Charles-pyt/My-Home-Assisant-Box/Checkout/Raspberry.png

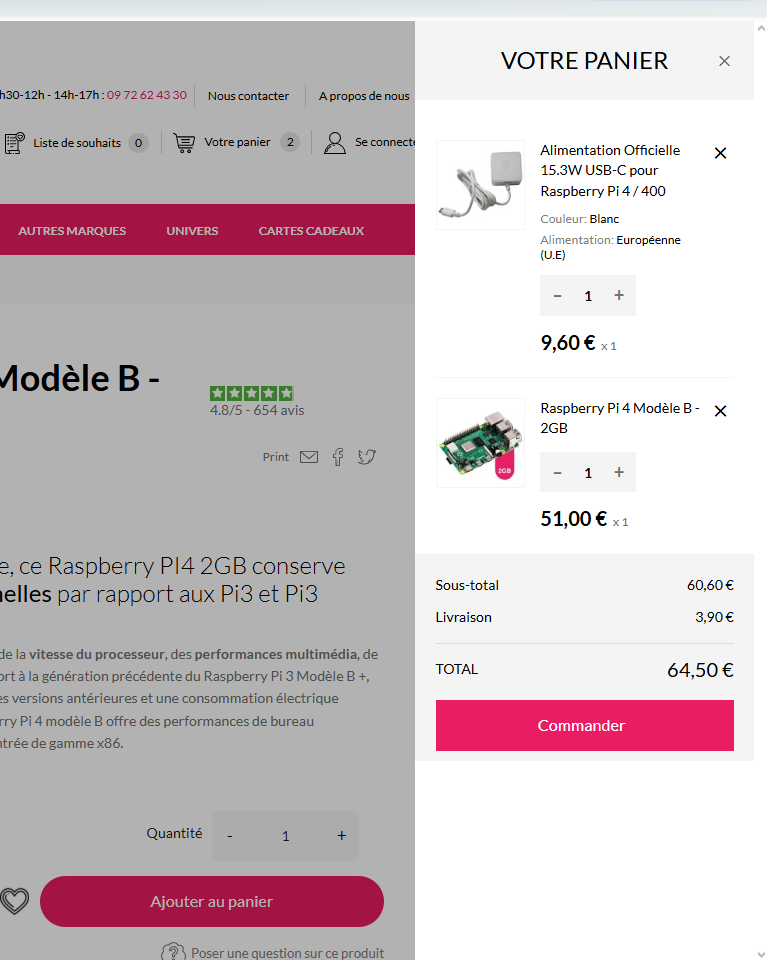
Checkout/Raspberry.png
