Charles-pyt/My-Home-Assisant-Box/Checkout/SD and FAN.png

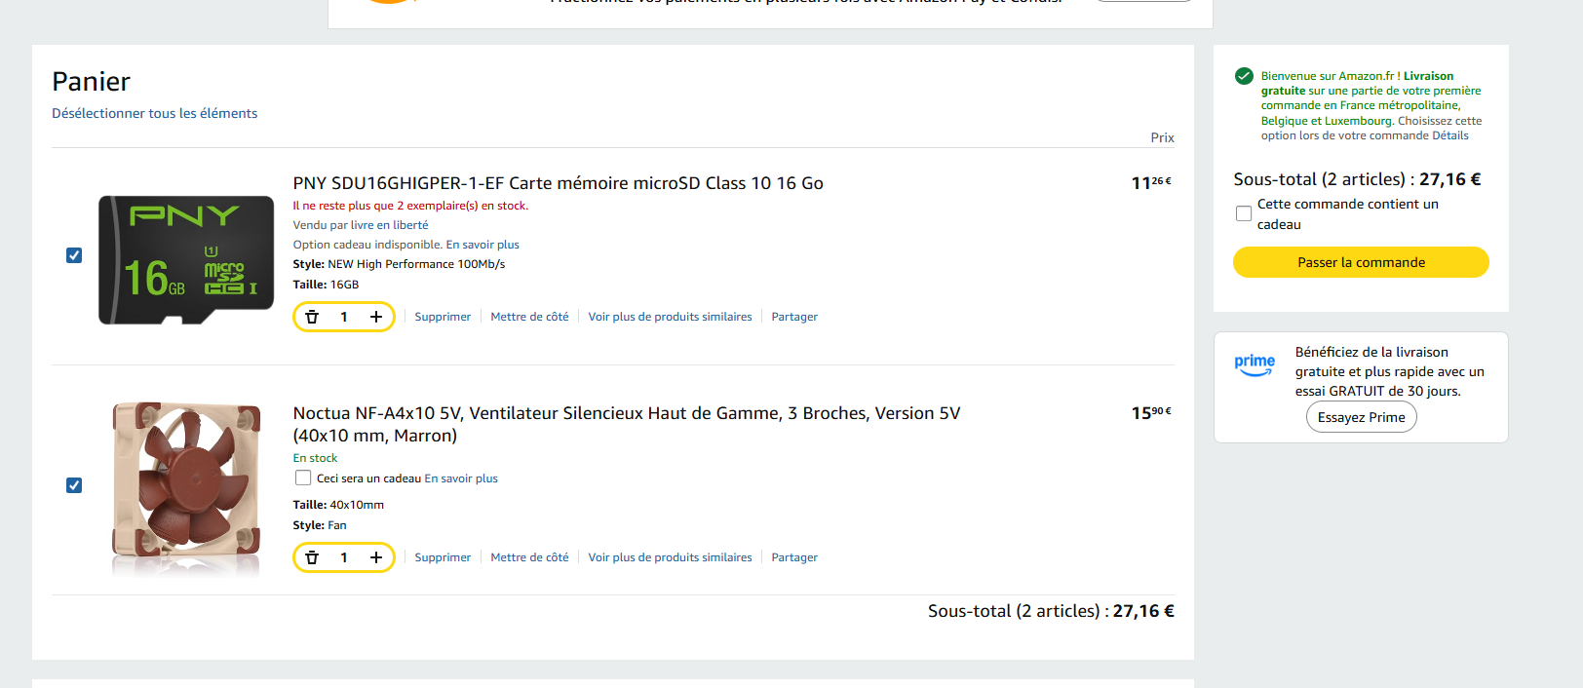
Checkout/SD and FAN.png
