Charles-pyt/My-Home-Assisant-Box/Checkout/Style.png

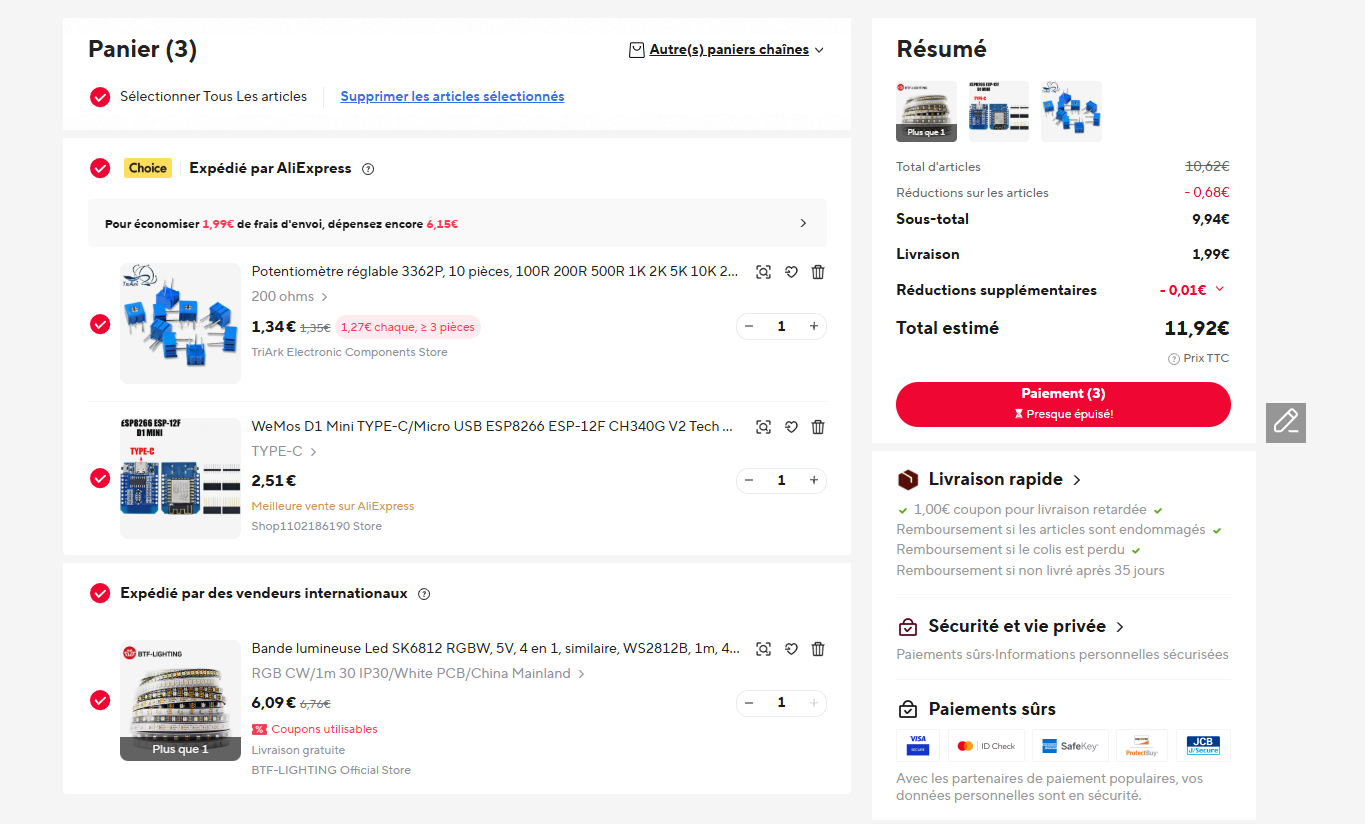
Checkout/Style.png
