Charles-pyt/My-Home-Assisant-Box/Checkout/Tools.png

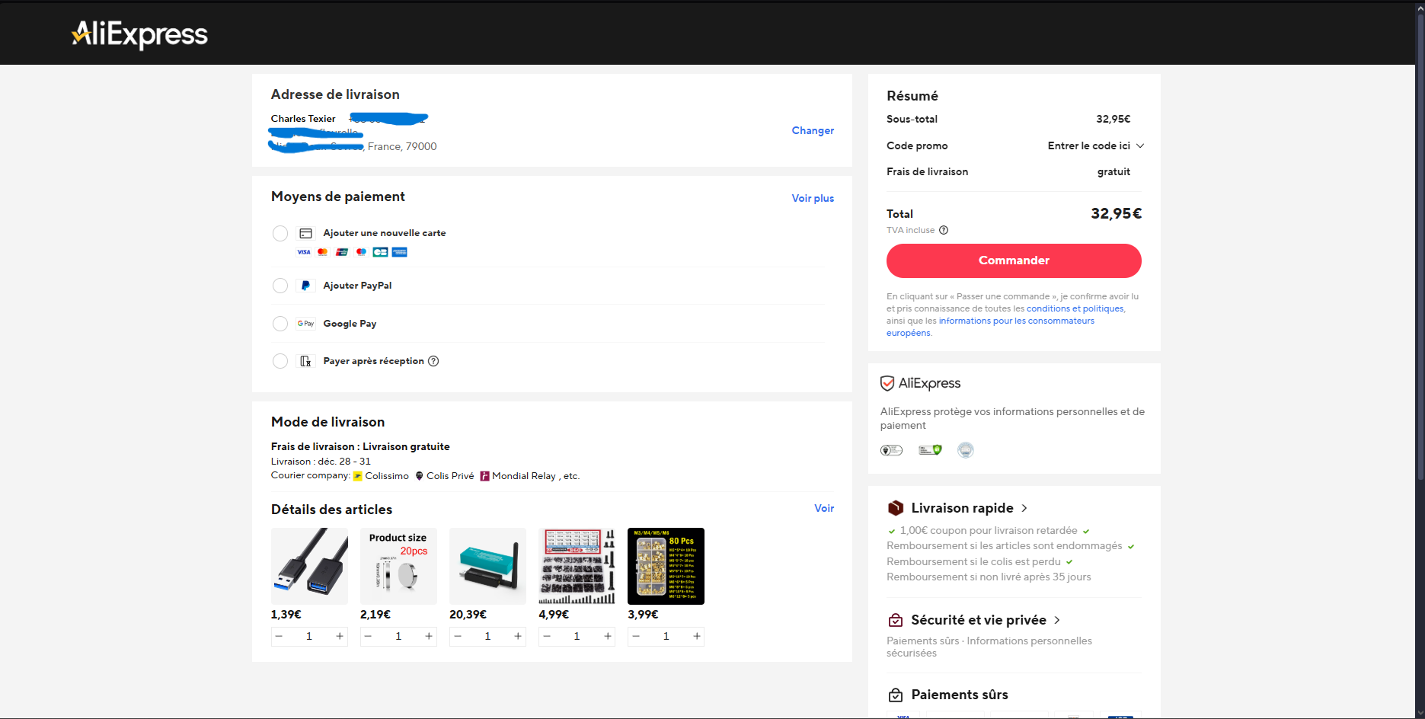
Checkout/Tools.png
