Charles-pyt/My-Home-Assisant-Box/images/Schéma.png

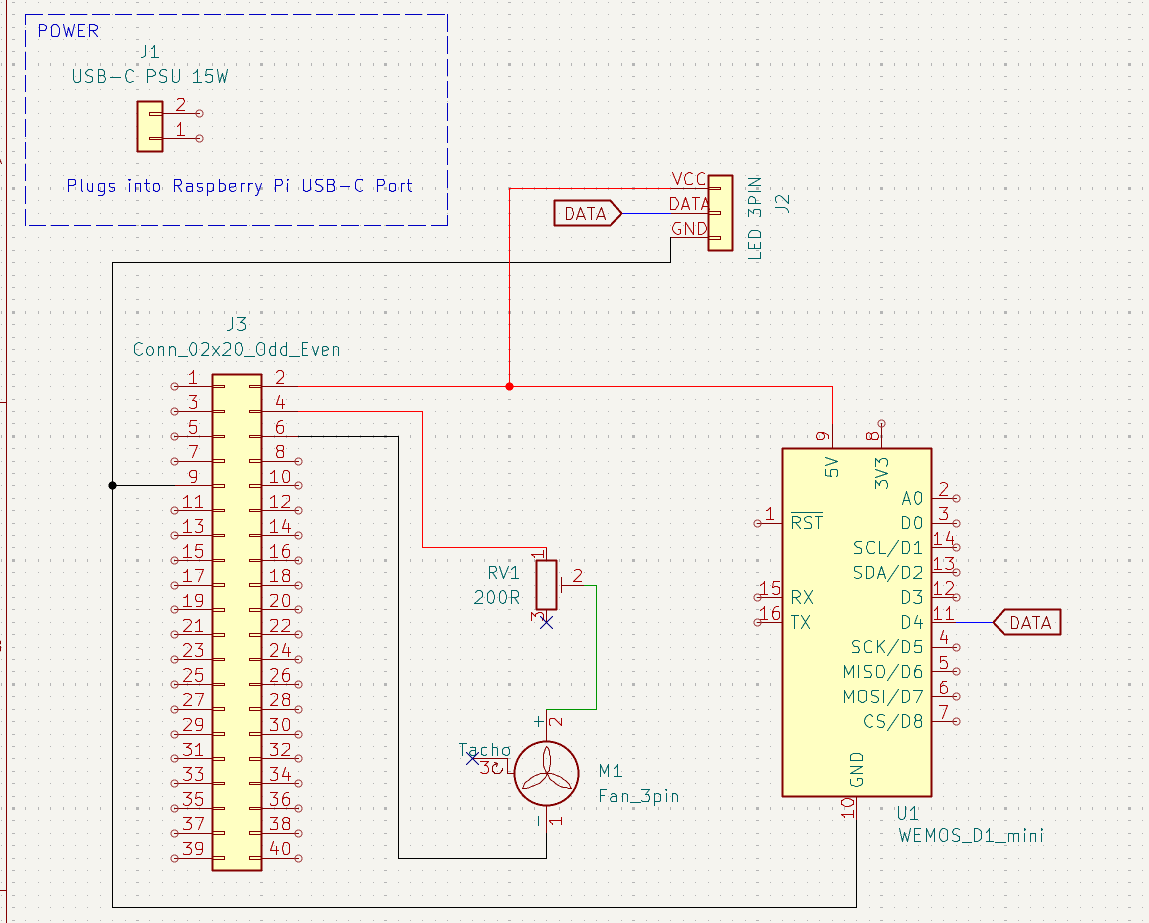
images/Schéma.png
