Charles-pyt/My-Home-Assisant-Box/images/Vue-éclatée.png

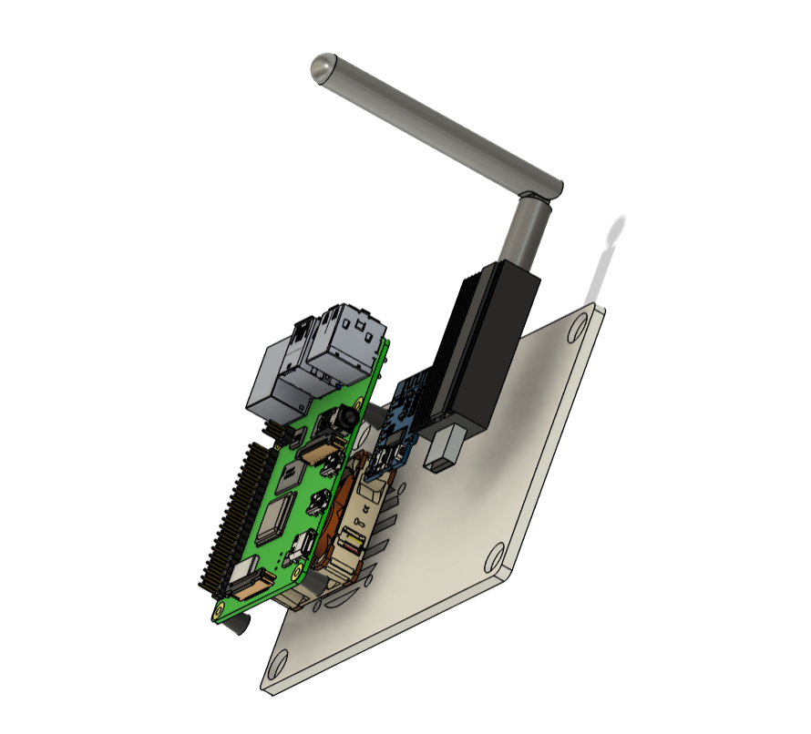
images/Vue-éclatée.png
