Charles-pyt/My-Home-Assisant-Box/images/BOM.png

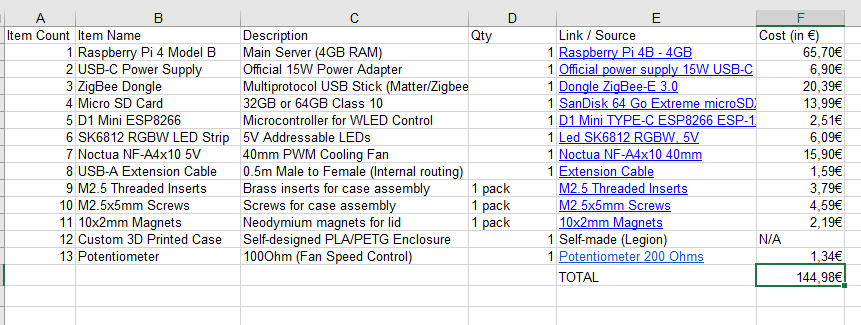
images/BOM.png
