Charles-pyt/My-Home-Assisant-Box/KiCad Schematic/Schematic.kicad_sch

## KiCad design KiCad Schematic/Schematic.kicad_sch (2025-12-26)

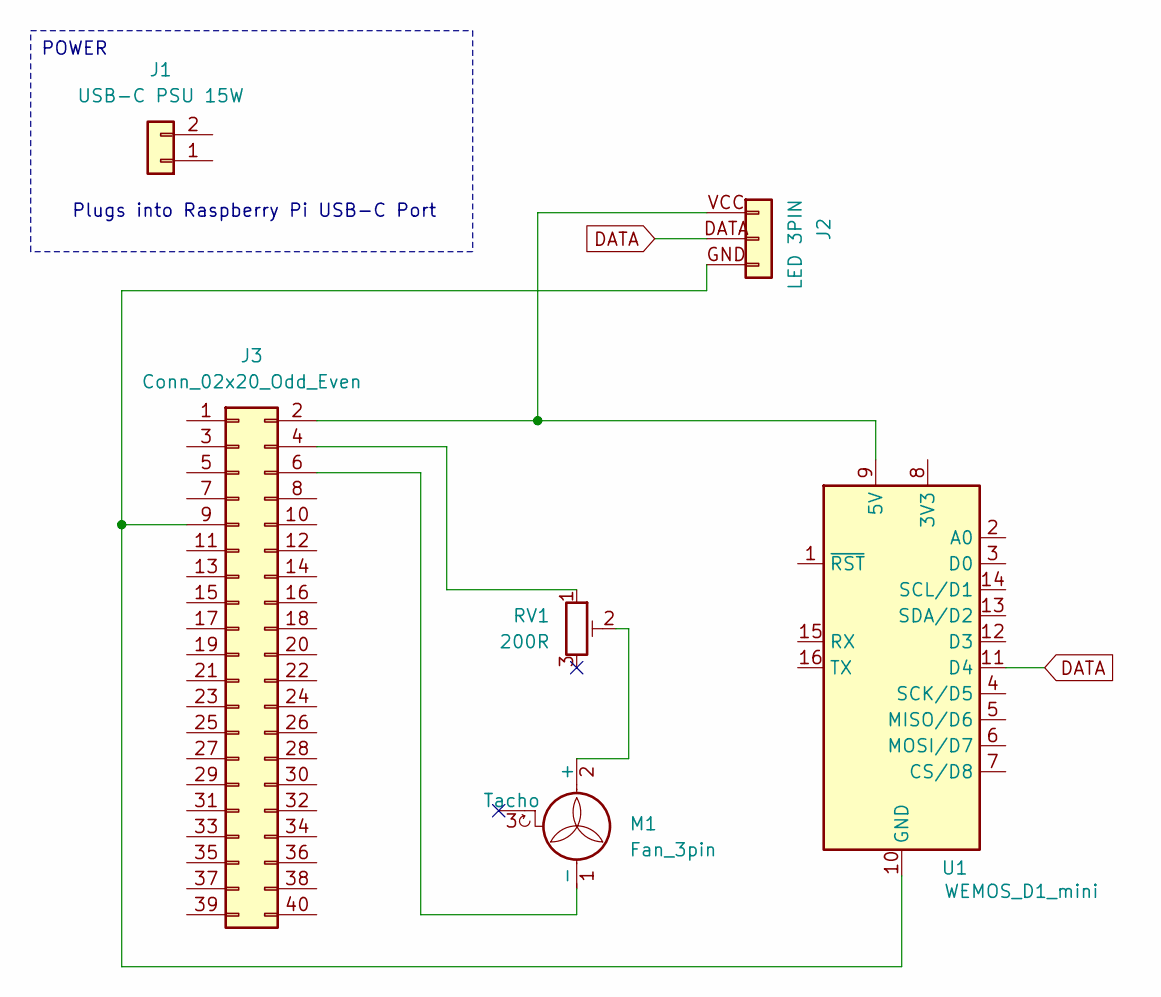
[picture p17: schematic Schematic.kicad_sch]

Parts:
J1: USB-C PSU 15W
J2: LED 3PIN
J3: Conn_02x20_Odd_Even
M1: Fan_3pin
RV1: 200R
U1: WEMOS_D1_mini; WEMOS_D1_mini_light

Connections:
DATA: J2.DATA (Pin_2), U1.11 (D4)
unnamed: J2.GND (Pin_3), J3.9, U1.10 (GND)
unnamed: J2.VCC (Pin_1), J3.2, U1.9 (5V)
unnamed: J3.4, RV1.1
unnamed: J3.6, M1.1 (-)
unnamed: M1.2 (+), RV1.2

Notes on the sheet:
Plugs into Raspberry Pi USB-C Port
POWER
